VxTi/space-defender/presentatie/Game presentatie.pptx

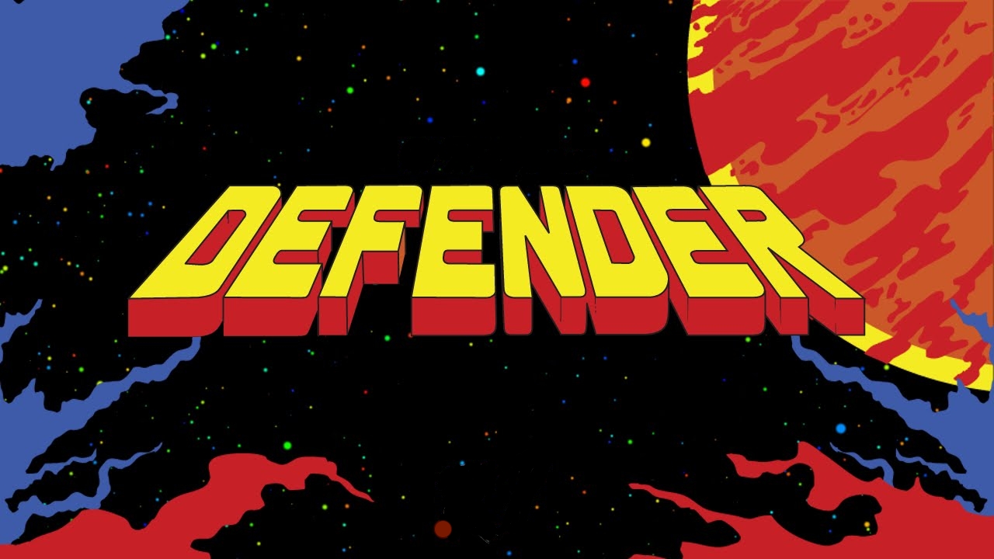
[picture p9: figure]

Gepresenteerd door
Just Koopen en Luca Warmenhoven

## Over ons spel

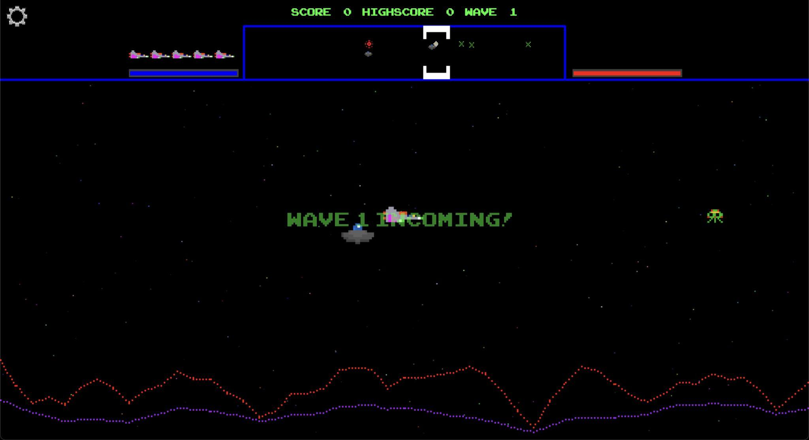
[picture p10: figure]

- Wat is Defender, en wat is het doel

- Hoe bestuur je het spel

- Backend + voorbeelden

- Gameplay (http://localhost:8080/)
