VxTi/space-defender/docs/assets/headers/game_controller_pcbs2.jpg

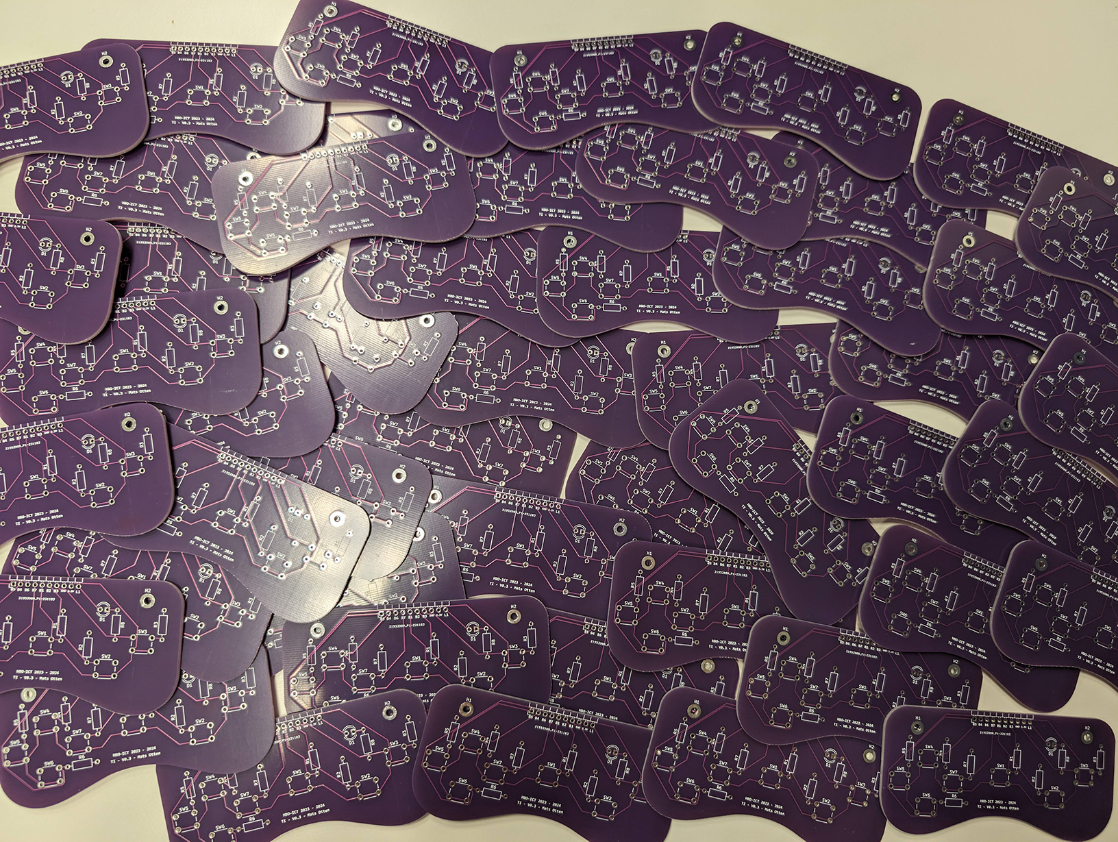
docs/assets/headers/game_controller_pcbs2.jpg
